noduino/CamGo/shell/dogy/dogy-00.jpg

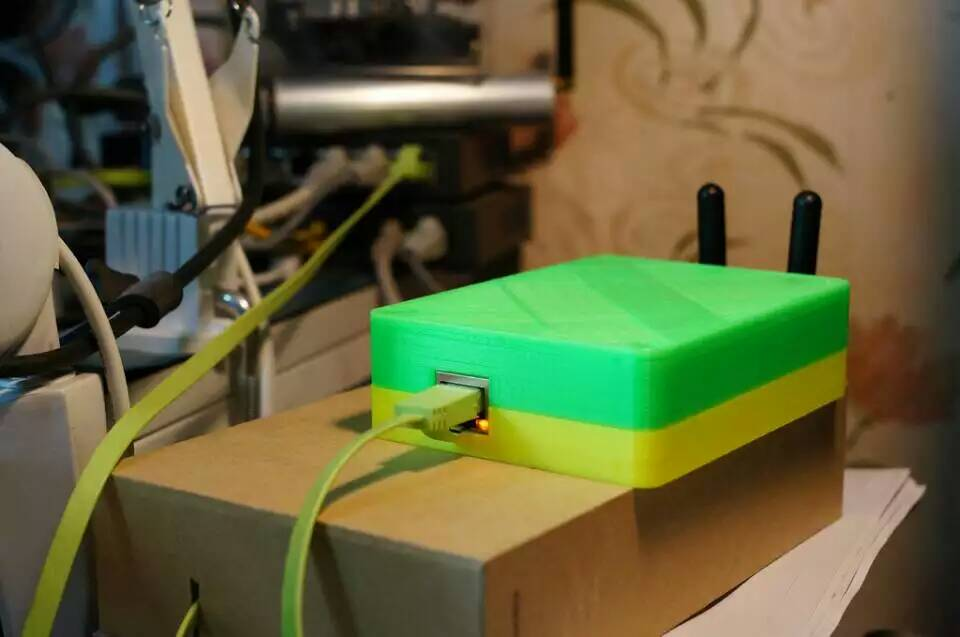
shell/dogy/dogy-00.jpg
