noduino/CamGo/shell/official/front-panel.png

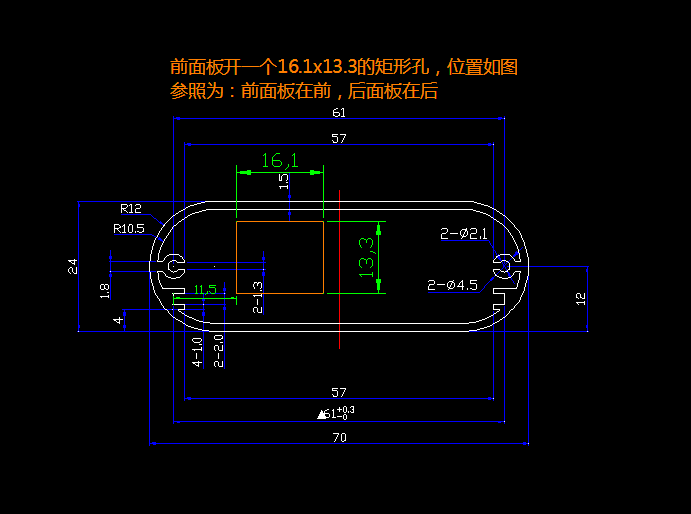
shell/official/front-panel.png
