noduino/CamGo/shell/official/rear-panel.png

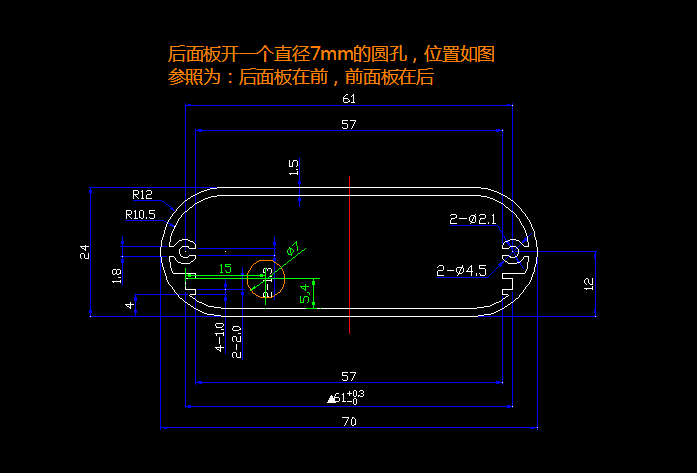
shell/official/rear-panel.png
